giuliovignati/butterworth_filter/spice_simulations/filter_real_values.asc

C1: cap; 78e-12
C2: cap; 103e-12
C3: cap; 306e-12
C4: cap; 803e-12
C5: cap; 48.8e-12
C6: cap; 912e-12
C7: cap; 95.2e-12
R1: res; 42.764e3
R2: res; 42.899e3
R3: res; 7.4425e3
R4: res; 7.4509e3
R5: res; 17.907e3
R6: res; 18.029e3
R7: res; 8.162e3
R8: res; 41.011e3
R10: res; 10.052e3
R11: res; 10.04e3
U1: TL072
U2: TL072
U3: TL072
U4: TL072
U5: TL072
V1: voltage; 0; AC 1 0
V2: voltage; 12
V3: voltage; -12
Named nets: 0, In, Out, Out_1, Out_2, Out_3, Out_4
.ac dec 10k 1 1Meg
.function uni(nom,tol) flat(nom*tol)+nom
